klemenjak/YoMoPie/rollback/roll/Images/1.jpeg

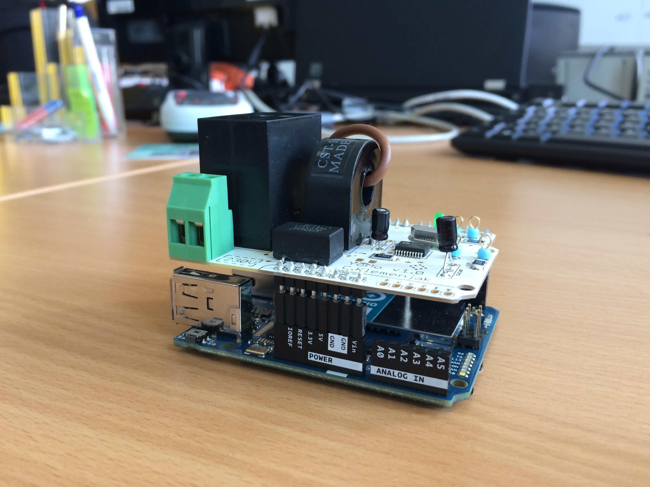
rollback/roll/Images/1.jpeg
