klemenjak/YoMoPie/firmware/exps/measurements_100Hzv2.csv

t | , |  | d | , | a | , | b
1521232876.545765 | 0.0032978057861328125 | 470775.861492007 | 155252.736
1521232876.55596 | 0.010195016860961914 | 47.00649410743434 | 47.9232
1521232876.566124 | 0.010164022445678711 | 47.14983684473739 | 47.9232
1521232876.576351 | 0.010226964950561523 | 57.67341560778646 | 58.9824
1521232876.586509 | 0.010158061981201172 | 54.43558043092522 | 55.296
1521232876.596736 | 0.010226964950561523 | 54.0688271322998 | 55.296
1521232876.60689 | 0.010154008865356445 | 50.82682188320928 | 51.6096
1521232876.61707 | 0.010179996490478516 | 50.69707052283479 | 51.6096
1521232876.627309 | 0.010239124298095703 | 46.80400257365063 | 47.9232
1521232876.637516 | 0.010206937789916992 | 50.56325517236224 | 51.6096
1521232876.647824 | 0.010308027267456055 | 53.643629925754595 | 55.296
1521232876.658211 | 0.010386943817138672 | 56.78513433631731 | 58.9824
1521232876.668393 | 0.010181903839111328 | 57.92865551669555 | 58.9824
1521232876.67856 | 0.010167121887207031 | 68.89029243185442 | 70.0416
1521232876.688726 | 0.010165929794311523 | 68.89837075128403 | 70.0416
1521232876.698931 | 0.01020503044128418 | 83.08373060505104 | 84.7872
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
