klemenjak/YoMoPie/firmware/exps/measurements_10Hz.csv

t | , |  | d | , | a | , | b
1521232809.166028 | 0.0024521350860595703 | 318949.2407846083 | 7821.06624
1521232809.266259 | 0.10023093223571777 | 56.639760534692044 | 56.77056
1521232809.366437 | 0.10017800331115723 | 75.06893481038705 | 75.20255999999999
1521232809.466597 | 0.10016012191772461 | 43.06192841441365 | 43.130880000000005
1521232809.566762 | 0.10016489028930664 | 48.5803756779983 | 48.66048
1521232809.666922 | 0.10016012191772461 | 43.06192841441365 | 43.130880000000005
1521232809.767084 | 0.10016179084777832 | 39.38076552559454 | 39.44447999999999
1521232809.867241 | 0.10015702247619629 | 55.9454330956345 | 56.03328
1521232809.9674 | 0.1001591682434082 | 50.791476099691025 | 50.87232
1521232810.067596 | 0.10019588470458984 | 36.42401093378259 | 36.49536
1521232810.1678 | 0.1002039909362793 | 44.14674464226741 | 44.236799999999995
1521232810.268006 | 0.10020613670349121 | 33.477231139309296 | 33.54624
1521232810.368215 | 0.10020899772644043 | 30.533306084476344 | 30.597119999999997
1521232810.468448 | 0.10023283958435059 | 36.778365406855734 | 36.864
1521232810.568661 | 0.10021305084228516 | 42.303472096382784 | 42.39359999999999
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
