klemenjak/YoMoPie/firmware/exps/measurements_500Hz.csv

t | , |  | d | , | a | , | b
1521232835.196216 | 0.012829065322875977 | 46722.70542821015 | 5994.086399999999
1521232835.296409 | 0.10019278526306152 | 45.62340479904055 | 45.71136
1521232835.396581 | 0.10017204284667969 | 61.089140503665334 | 61.19423999999999
1521232835.496748 | 0.10016703605651855 | 48.94736025965234 | 49.02911999999999
1521232835.596915 | 0.10016703605651855 | 32.754248594804956 | 32.80896
1521232835.697087 | 0.10017204284667969 | 43.05680384896895 | 43.130880000000005
1521232835.797254 | 0.10016703605651855 | 40.114753897008306 | 40.18175999999999
1521232835.897424 | 0.10016989707946777 | 66.24265566266725 | 66.3552
1521232835.997619 | 0.10019493103027344 | 56.66011186019684 | 56.77056
1521232836.097834 | 0.10021519660949707 | 31.634962632998125 | 31.70304
1521232836.198065 | 0.10023093223571777 | 44.13487833872107 | 44.236799999999995
1521232836.298303 | 0.10023784637451172 | 56.26808839175317 | 56.40192
1521232836.398601 | 0.10029816627502441 | 51.82371914704015 | 51.97823999999999
1521232836.498763 | 0.10016202926635742 | 75.44895061883791 | 75.57119999999999
1521232836.598924 | 0.10016083717346191 | 66.24864754782733 | 66.3552
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
