klemenjak/YoMoPie/firmware/exps/measurements_500Hzv2.csv

t | , |  | d | , | a | , | b
1521232895.478852 | 0.0008320808410644531 | 815669.6687448756 | 339351.55199999997
1521232895.481889 | 0.003036975860595703 | 60.69195425341498 | 92.16
1521232895.484748 | 0.002858877182006836 | 51.578291270452844 | 73.728
1521232895.4875 | 0.002752065658569336 | 53.58011700805683 | 73.728
1521232895.490167 | 0.002666950225830078 | 55.29012074235652 | 73.728
1521232895.492885 | 0.002718210220336914 | 54.2474599266731 | 73.728
1521232895.495728 | 0.0028429031372070312 | 51.86810555384099 | 73.728
1521232895.498461 | 0.002732992172241211 | 40.4655385124313 | 55.29600000000001
1521232895.501266 | 0.002804994583129883 | 52.5690854759031 | 73.728
1521232895.504056 | 0.0027899742126464844 | 39.639076052640576 | 55.29600000000001
1521232895.506829 | 0.0027730464935302734 | 39.88104788651019 | 55.29600000000001
1521232895.509889 | 0.003059864044189453 | 48.190376392706874 | 73.728
1521232895.513175 | 0.003286123275756836 | 44.8723275501705 | 73.728
1521232895.516302 | 0.0031270980834960938 | 35.365695941445566 | 55.29600000000001
1521232895.519625 | 0.0033228397369384766 | 44.37650072641171 | 73.728
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
