klemenjak/YoMoPie/rollback/roll/PCB/[WiP]-YoMoPie_3phase/schematic_3phase.sch

## EAGLE design rollback/roll/PCB/[WiP]-YoMoPie_3phase/schematic_3phase.sch (2017-11-27)

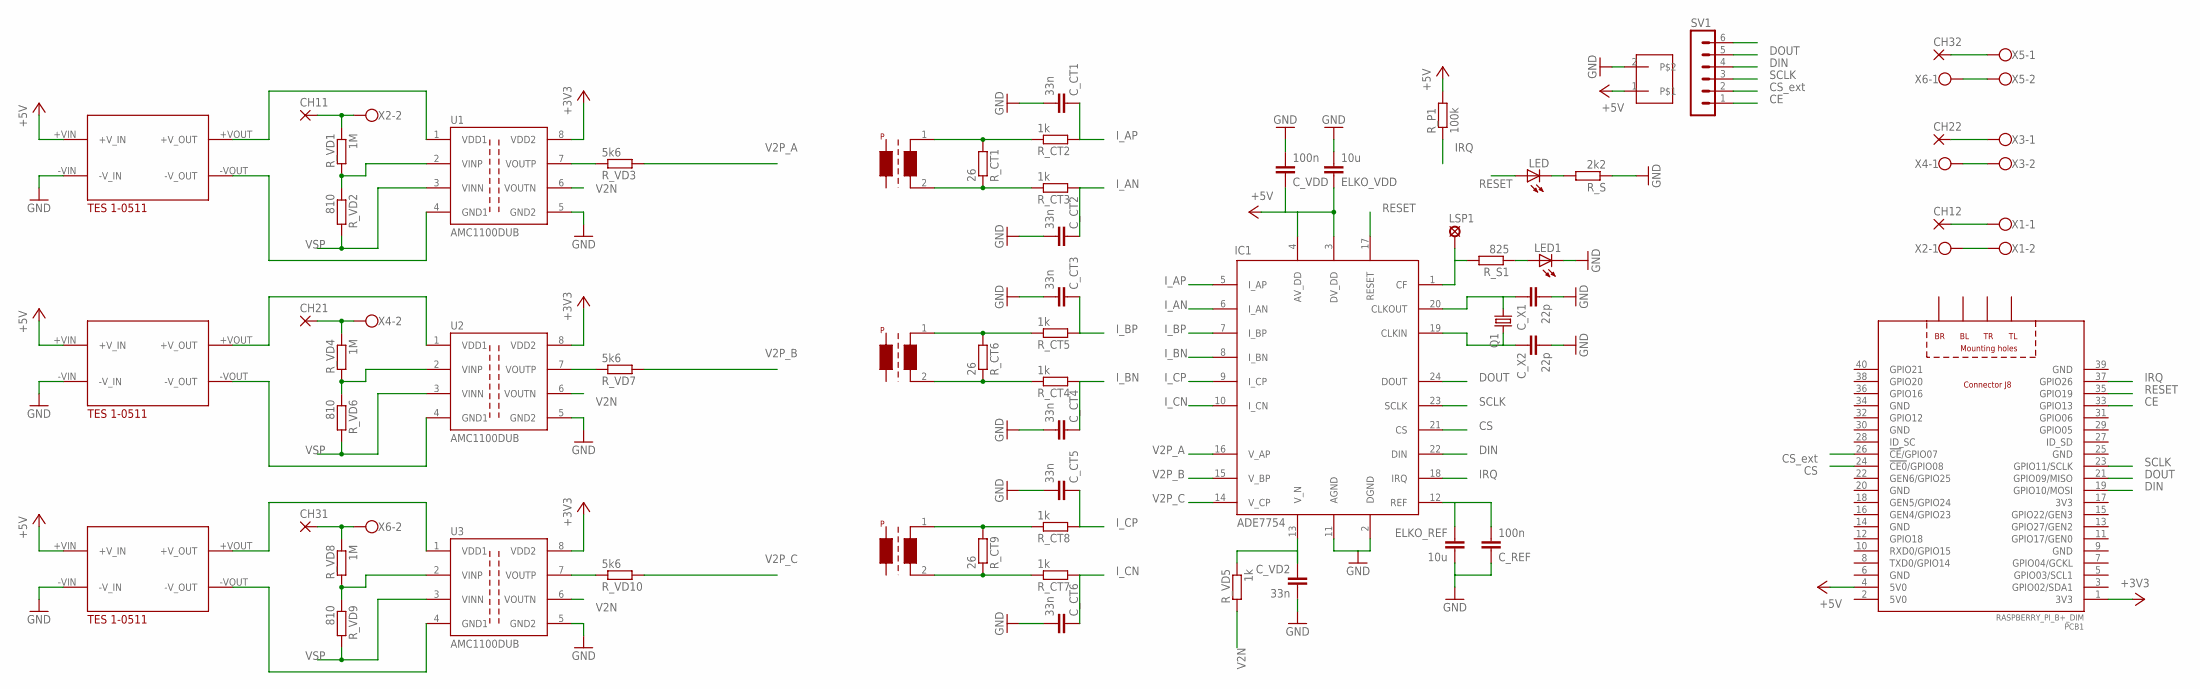
[picture p9: schematic schematic_3phase.sch]

Parts:
CH11, CH12, CH21, CH22, CH31, CH32: WIREPAD3,81/1,4; 3,81/1,4
C_CT1, C_CT2, C_CT3, C_CT4, C_CT5, C_CT6: 33n; C1206K
C_REF: 100n; C1206K
C_VD2: 33n; C1206K
C_VDD: 100n; C1206K
C_X1, C_X2: 22p; C1206K
ELKO_REF: 10u; C7.5B3
ELKO_VDD: 10u; C7.5B3
IC1: ADE7754; SO24L
LED, LED1: LED3MM
LSP1: LSP10
PCB1: RASPBERRY_PI_B+_DIM; RASPBERRY_PI_BPLUS_DIM
Q1: CRYSTALHC18U-V; HC18U-V
R_CT1, R_CT6, R_CT9: 26; R2512
R_CT2, R_CT3, R_CT4, R_CT5, R_CT7, R_CT8: 1k; R2010
R_P1: 100k; R2010
R_S: 2k2; R2512
R_S1: 825; R2512
R_VD1, R_VD4, R_VD8: 1M; R2512
R_VD2, R_VD6, R_VD9: 810; R2512
R_VD3, R_VD7, R_VD10: 5k6; R2512
R_VD5: 1k; R2010
SV1: MA06-1
U1, U2, U3: AMC1100DUB; DIP8-GULLWING
U$1: 2-PINHEAD
U$2, U$6, U$7: CST-1020; CST1020
U$3, U$4, U$5: TES1-0511; 0511
X1, X2, X3, X4, X5, X6: W237-102

Connections:
+3V3: PCB1.1 (3V3), U1.8 (VDD2), U2.8 (VDD2), U3.8 (VDD2)
+5V: C_VDD.1, ELKO_VDD.1, IC1.3 (DV_DD), IC1.4 (AV_DD), PCB1.4 (5V0), R_P1.2, U$1.1, U$3.+VIN (+V_IN), U$4.+VIN (+V_IN), U$5.+VIN (+V_IN)
CE: PCB1.33 (GPIO13), SV1.1
CS: IC1.21 (CS), PCB1.24 (!CE0!/GPIO08)
CSE: PCB1.26 (!CE!/GPIO07), SV1.2
DIN: IC1.22 (DIN), PCB1.19 (GPIO10/MOSI), SV1.4
DOUT: IC1.24 (DOUT), PCB1.21 (GPIO09/MISO), SV1.5
GND: C_CT1.2, C_CT2.2, C_CT3.2, C_CT4.2, C_CT5.2, C_CT6.2, C_REF.1, C_VD2.2, C_VDD.2, C_X1.2, C_X2.2, ELKO_REF.2, ELKO_VDD.2, IC1.2 (DGND), IC1.11 (AGND), LED1.K (C), R_S.1, U1.5 (GND2), U2.5 (GND2), U3.5 (GND2), U$1.2, U$3.-VIN (-V_IN), U$4.-VIN (-V_IN), U$5.-VIN (-V_IN)
IRQ: IC1.18 (IRQ), PCB1.37 (GPIO26), R_P1.1
I_AN: C_CT2.1, IC1.6 (I_AN), R_CT3.2
I_AP: C_CT1.1, IC1.5 (I_AP), R_CT2.2
I_BN: C_CT4.1, IC1.8 (I_BN), R_CT4.2
I_BP: C_CT3.1, IC1.7 (I_BP), R_CT5.2
I_CN: C_CT6.1, IC1.10 (I_CN), R_CT7.2
I_CP: C_CT5.1, IC1.9 (I_CP), R_CT8.2
unnamed: C_REF.2, ELKO_REF.1, IC1.12 (REF)
unnamed: X1.2, X2.1
unnamed: C_VD2.1, IC1.13 (V_N), R_VD5.1
unnamed: CH12.1, X1.1
unnamed: X3.2, X4.1
unnamed: CH22.1, X3.1
unnamed: IC1.1 (CF), LSP1.MP, R_S1.2
unnamed: CH11.1, R_VD1.1, X2.2
unnamed: X5.2, X6.1
unnamed: LED1.A, R_S1.1
unnamed: CH32.1, X5.1
unnamed: R_VD1.2, R_VD2.1, U1.2 (VINP)
unnamed: R_VD4.2, R_VD6.1, U2.2 (VINP)
unnamed: R_VD7.1, U2.7 (VOUTP)
unnamed: R_CT1.2, R_CT2.1, U$2.1
unnamed: U2.1 (VDD1), U$4.+VOUT (+V_OUT)
unnamed: U2.4 (GND1), U$4.-VOUT (-V_OUT)
unnamed: CH21.1, R_VD4.1, X4.2
unnamed: R_VD8.2, R_VD9.1, U3.2 (VINP)
unnamed: R_VD10.1, U3.7 (VOUTP)
unnamed: U3.1 (VDD1), U$5.+VOUT (+V_OUT)
unnamed: U3.4 (GND1), U$5.-VOUT (-V_OUT)
unnamed: R_VD3.1, U1.7 (VOUTP)
unnamed: CH31.1, R_VD8.1, X6.2
unnamed: LED.K (C), R_S.2
unnamed: R_CT4.1, R_CT6.1, U$6.2
unnamed: R_CT5.1, R_CT6.2, U$6.1
unnamed: R_CT7.1, R_CT9.1, U$7.2
unnamed: R_CT8.1, R_CT9.2, U$7.1
unnamed: U1.1 (VDD1), U$3.+VOUT (+V_OUT)
unnamed: U1.4 (GND1), U$3.-VOUT (-V_OUT)
unnamed: R_CT1.1, R_CT3.1, U$2.2
unnamed: C_X1.1, IC1.20 (CLKOUT), Q1.1
unnamed: C_X2.1, IC1.19 (CLKIN), Q1.2
RESET: IC1.17 (RESET), LED.A, PCB1.35 (GPIO19)
SCLK: IC1.23 (SCLK), PCB1.23 (GPIO11/SCLK), SV1.3
V2N: R_VD5.2, U1.6 (VOUTN), U2.6 (VOUTN), U3.6 (VOUTN)
V2P_A: IC1.16 (V_AP), R_VD3.2
V2P_B: IC1.15 (V_BP), R_VD7.2
V2P_C: IC1.14 (V_CP), R_VD10.2
VSP: R_VD2.2, R_VD6.2, R_VD9.2, U1.3 (VINN), U2.3 (VINN), U3.3 (VINN)

Notes on the sheet:
RESET
IRQ
DOUT
DIN
SCLK
V2P_A
CS_ext
V2P_C
V2P_B
I_CN
I_CP
I_BN
I_BP
I_AN
I_AP
